d-send/Wearable-Smart-Alarm-Armband/20260225_041829.jpg

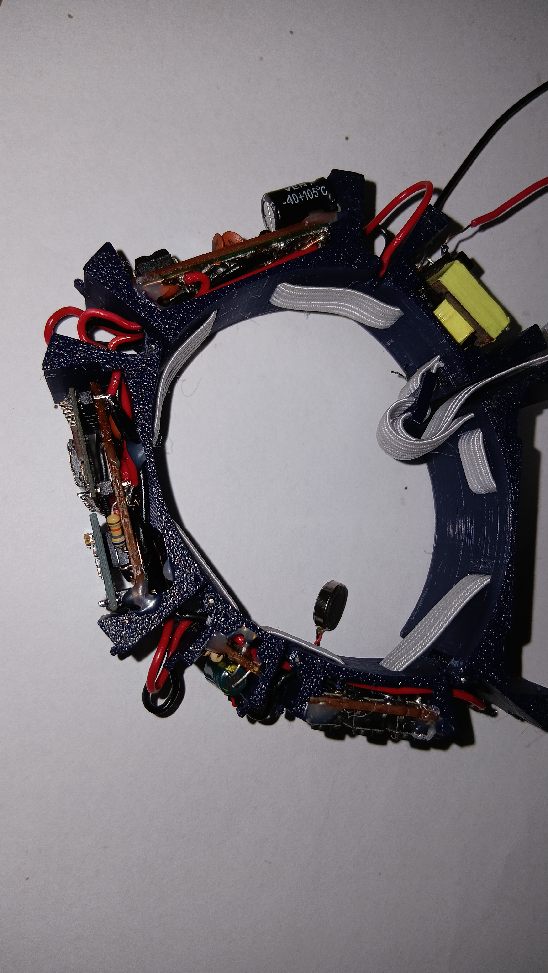
20260225_041829.jpg
