d-send/Wearable-Smart-Alarm-Armband/20260225_041835.jpg

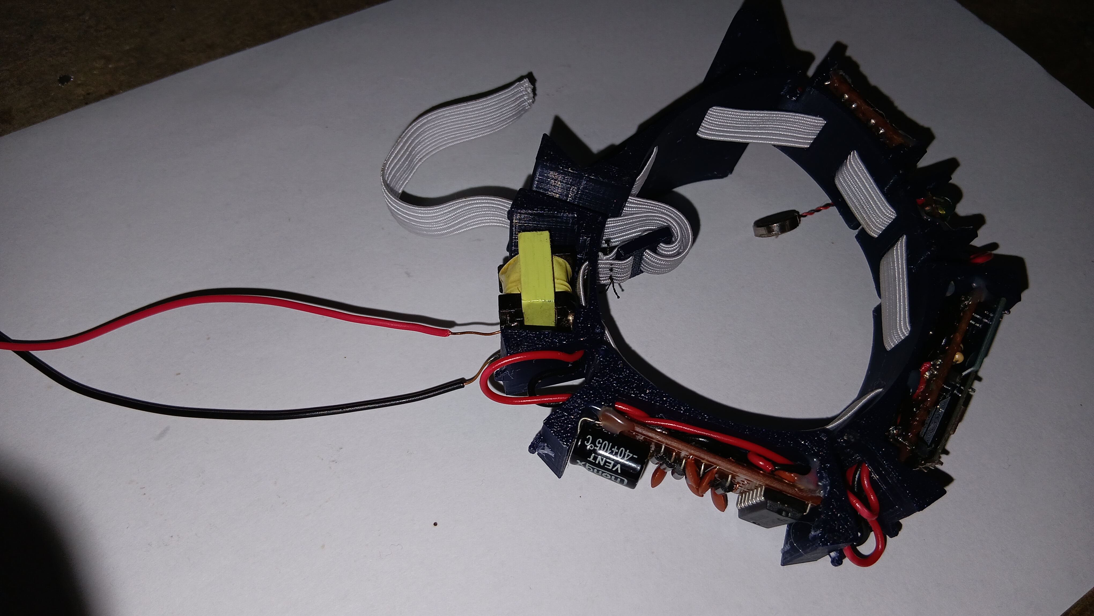
20260225_041835.jpg
