d-send/Wearable-Smart-Alarm-Armband/20260225_041847.jpg

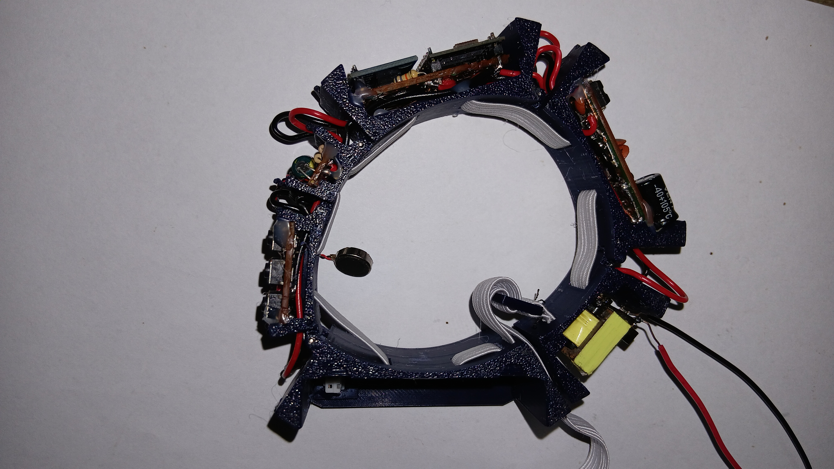
20260225_041847.jpg
