d-send/Wearable-Smart-Alarm-Armband/20260320_060355.jpg

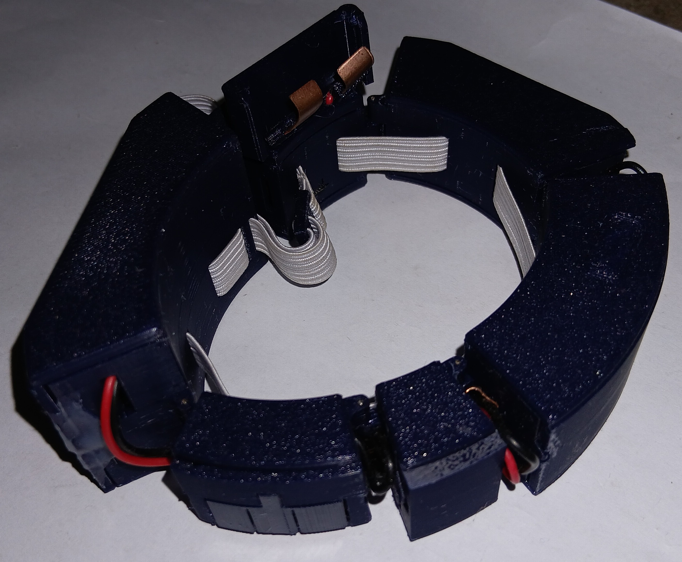
20260320_060355.jpg
