d-send/Wearable-Smart-Alarm-Armband/20260320_060510.jpg

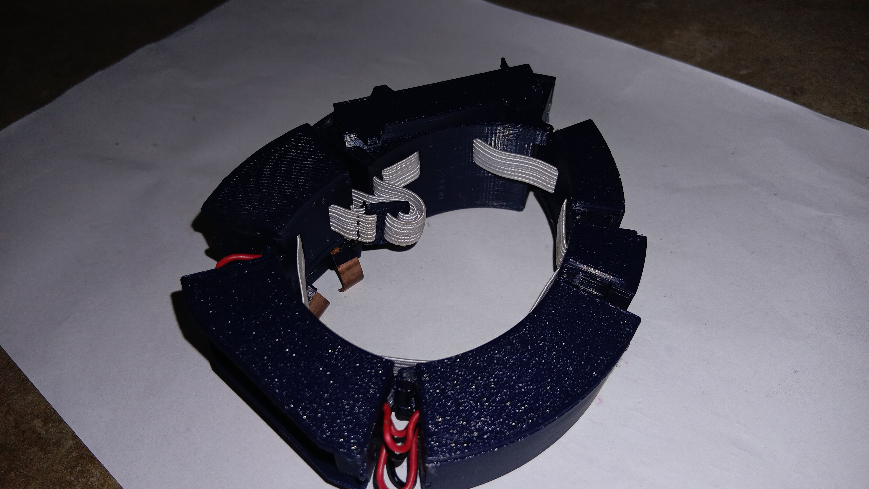
20260320_060510.jpg
